gbertoldo/rRocket-Monitor/src/Barometer.cpp

/*
  The MIT License (MIT)

  Copyright (C) 2022 Guilherme Bertoldo and Jonas Joacir Radtke
  (UTFPR) Federal University of Technology - Parana

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
*/

#include "Barometer.h"

bool Barometer::begin()
{

  Wire.begin();

  if ( searchBarometerAddress )
  {

    // Searching for barometer address
    if ( ! getBarometerAddress(barometerAddress) ) return false;

  }

  // Initializing BMP
  if (!barometer.begin(barometerAddress)) return false;

  baseline = barometer.readAltitude(1013.25);

  return true;
}


float Barometer::getAltitude()
{

  float altitude = 0.0;
  
  altitude = barometer.readAltitude();

  altitude -= baseline;

  return altitude;

}


void Barometer::setBaseline(float baseline)
{
   
   this->baseline = this->baseline + baseline;
   
}


bool Barometer::getBarometerAddress(byte& address)
{

  byte err;
  int  counter {0};

  for (byte addr = 1; addr < 127; addr++ )
  {

    Wire.beginTransmission(addr);

    err = Wire.endTransmission();

    if (err == 0)
    {
      counter++;

      address = addr;
    }

  }

  if ( counter != 1 ) return false;

  return true;

};
